8BitMixtape/8Bit_JogjaNoise/Jogjarmageddon_PartsPlacement.jpg

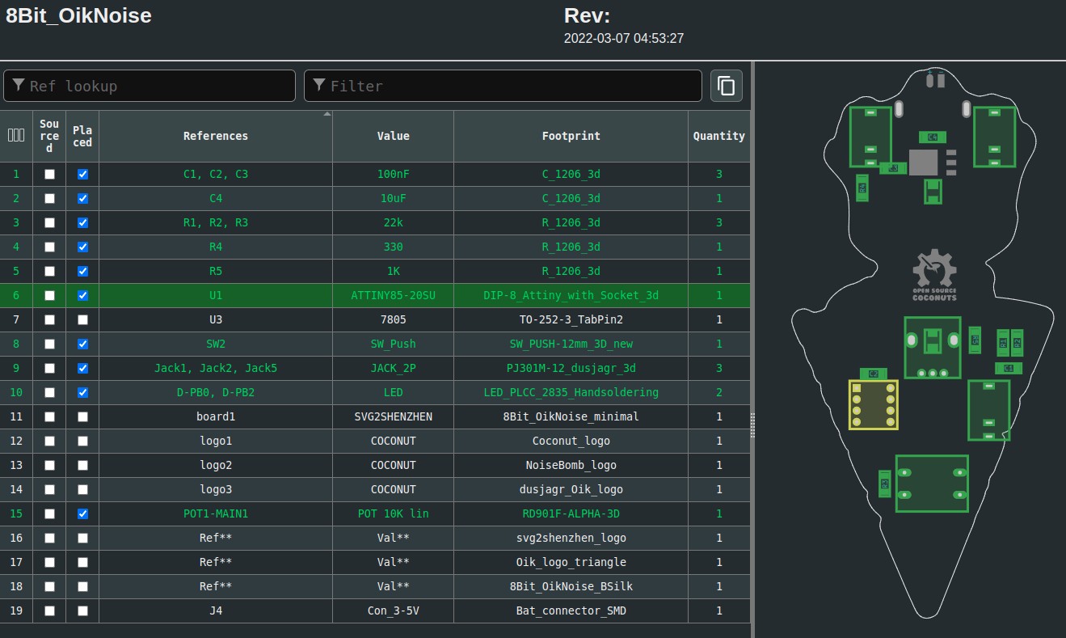
Jogjarmageddon_PartsPlacement.jpg
