8BitMixtape/8Bit_JogjaNoise/photos/jarmaggedon-BOM.jpg

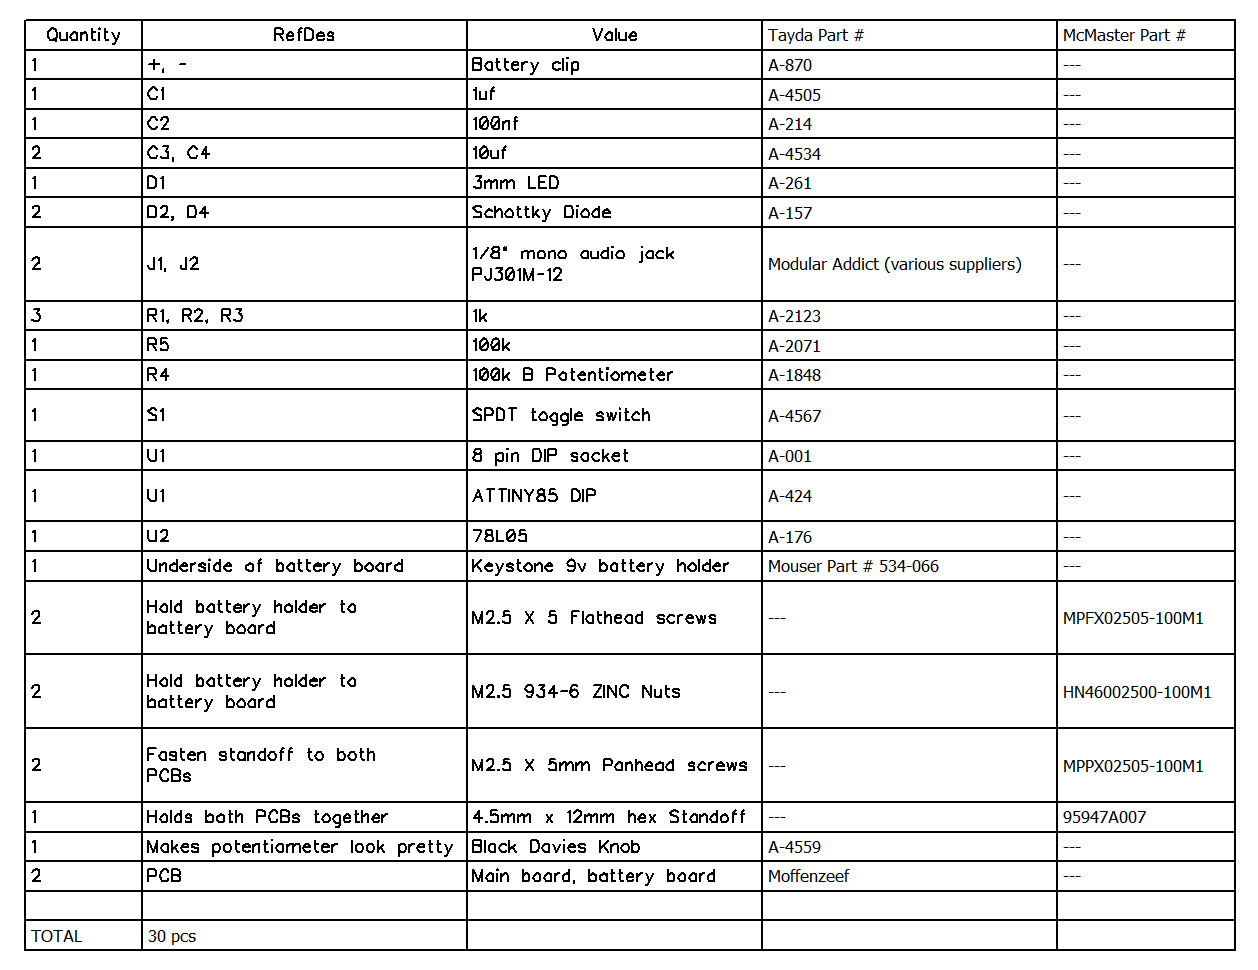
photos/jarmaggedon-BOM.jpg
