8BitMixtape/8Bit_JogjaNoise/NoiseCode/MiniDrone_v2/MiniDrone_v2.ino

#include <Arduino.h>
#line 1 "/Users/xcorex/Documents/Arduino/MiniDrone/MiniDrone.ino"
#line 1 "/Users/xcorex/Documents/Arduino/MiniDrone/MiniDrone.ino"
///////////////////////////////////////////////////
//                  __ __                        //
//  .---.-.--.--.--|  |__|.-----.                //
//  |  _  |  |  |  _  |  ||  _  |                //
//  |___._|_____|_____|__||_____|                //
//   __                __     __         __      //
//  |  |--.---.-.----.|  |--.|  |.---.-.|  |--.  //
//  |     |  _  |  __||    < |  ||  _  ||  _  |  // 
//  |__|__|___._|____||__|__||__||___._||_____|  //
//                                               //
///////////////////////////////////////////////////
//  MiniDrone                                    //
//  Minimal Drone Machine                        //
//  Pangrus 2017                                 //
//  Sound generation based on "Tiny Synth v4"    //
//  by David Johnson-Davies                      //
//  http://www.technoblogy.com                   //
//  CC Attribution 4.0 International license:    //
//  http://creativecommons.org/licenses/by/4.0/  //
///////////////////////////////////////////////////

#include <avr/power.h>

int frequenza1;
int frequenza2;
int Acc[]   = {0, 0, 0, 0};
int Freqs[] = {0, 0, 0, 0};

// Genera quattro onde triangolari a diverse frequenze
#line 41 "/Users/xcorex/Documents/Arduino/MiniDrone/MiniDrone.ino"
void setup();
#line 60 "/Users/xcorex/Documents/Arduino/MiniDrone/MiniDrone.ino"
void loop();
#line 30 "/Users/xcorex/Documents/Arduino/MiniDrone/MiniDrone.ino"

ISR(TIMER0_COMPA_vect) {
  signed char Mask, Temp, Sum=0;
  for (int c=0; c<4; c++) {
    Acc[c] = Acc[c] + Freqs[c];
    Temp = Acc[c] >> 8;
    Mask = Temp >> 15;
    Sum = Sum + ((char)(Temp ^ Mask) >> 1);
  }
  OCR1A = Sum;
}

void setup() {
  clock_prescale_set(clock_div_2); //NO PROCESSOR PRESCALE

  //START PLL ENABLE
  PLLCSR |= (1 << PLLE);               // Enable PLL (64 MHz)
  _delay_us(100);                      // Wait for a steady state
  while (!(PLLCSR & (1 << PLOCK)));    // Ensure PLL lock: do nothing while the bit PLOCK in register PLLCSR is false
  PLLCSR |= (1 << PCKE);               // Enable PLL as clock source for timer 1
  //END PLL ENABLE
  
  pinMode(1, OUTPUT);                                // Pin 6 corrisponde a OC1A,PB1
  TCCR0A = 0;                                        // Reset del TCCR0A registro di controllo dei timer
  TCCR0B = 0;                                        // Reset del TCCR0B registro di controllo dei timer
  TIMSK = 1<<OCIE0A;                                 // Setto OCIEOA per abilitare l'interrupt del timer 0
  TCCR0A = 1<<WGM00 | 1<<WGM01;                      // Fast PWM
  TCCR0B = 1<<WGM02 | 1<<CS02| 0<<CS01 | 0<<CS00;    // Fast PWM | Setto CS02 per avere fClock/256 = 8000KHz / 256 = 31.250 KHz  
  TCCR1  = 1<<PWM1A | 2<<COM1A0 | 1<<CS10;           // Set up Watchdog timer for 8 Hz interrupt for ticks timer.
}

void loop() {
 frequenza1 = analogRead (A2) + 100;
 frequenza2 = analogRead (A1) + 100;


// Rapporti tra frequenze
// 1/1 Unisono
// 5/4 Terza
// 4/3 Quarta
// 3/2 Quinta
// 2/1 Ottava

 Freqs[0] = frequenza1; 
 Freqs[1] = frequenza2;
 Freqs[2] = frequenza1*5/4;
 Freqs[3] = frequenza2*3/2;
 }
